keloGuo/magicKey63FW/image/PCB反面.jpg

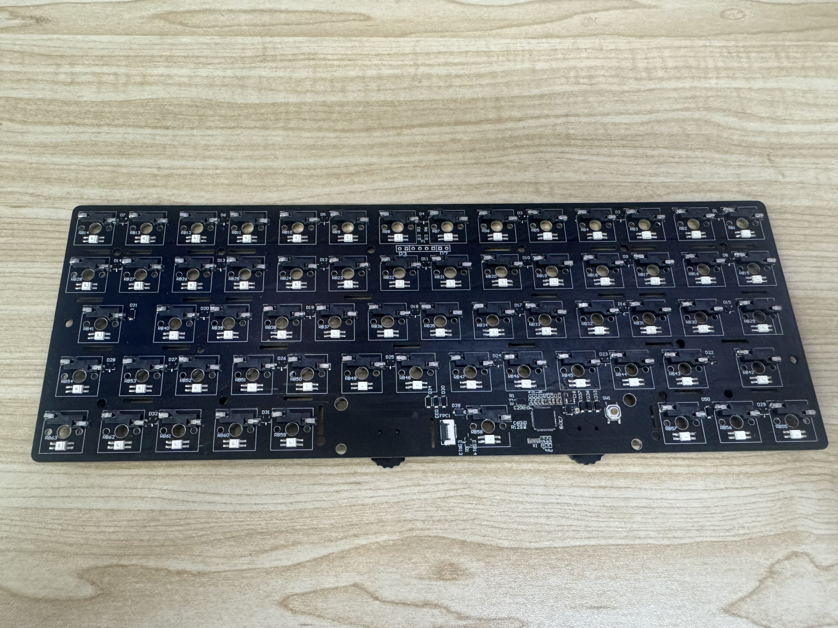
image/PCB反面.jpg
