keloGuo/magicKey63FW/image/web宏编辑页.png

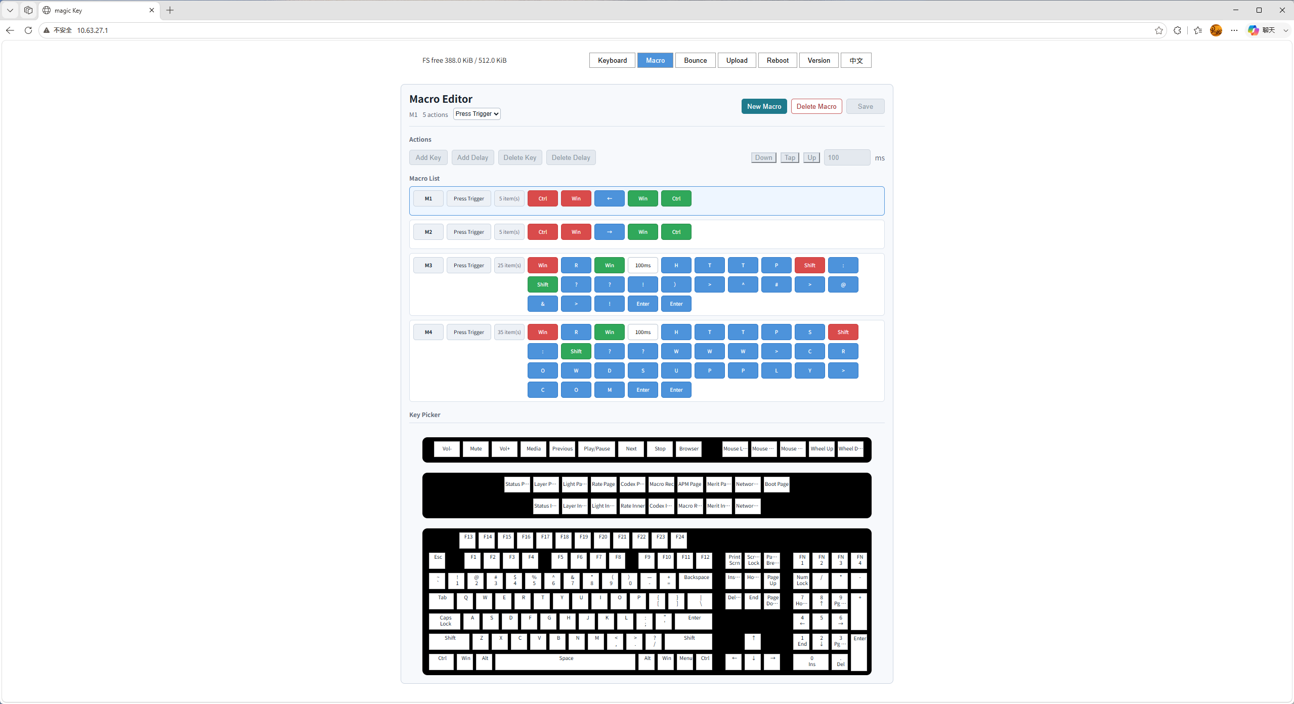
image/web宏编辑页.png
