keloGuo/magicKey63FW/image/定位板正面.jpg

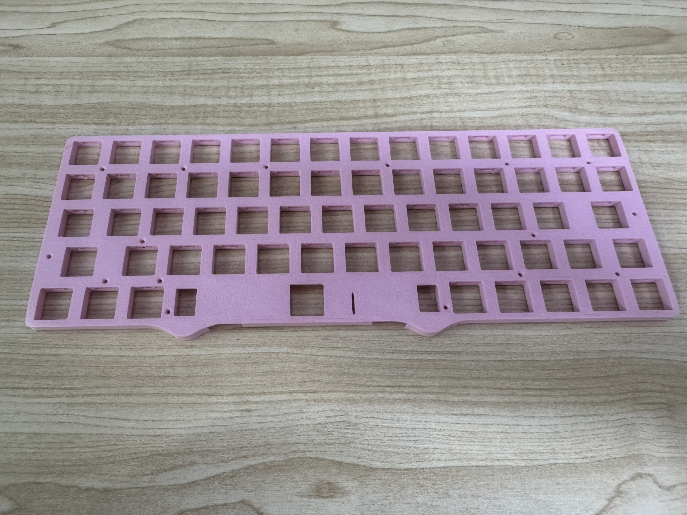
image/定位板正面.jpg
