keloGuo/magicKey63FW/image/定位板背面.jpg

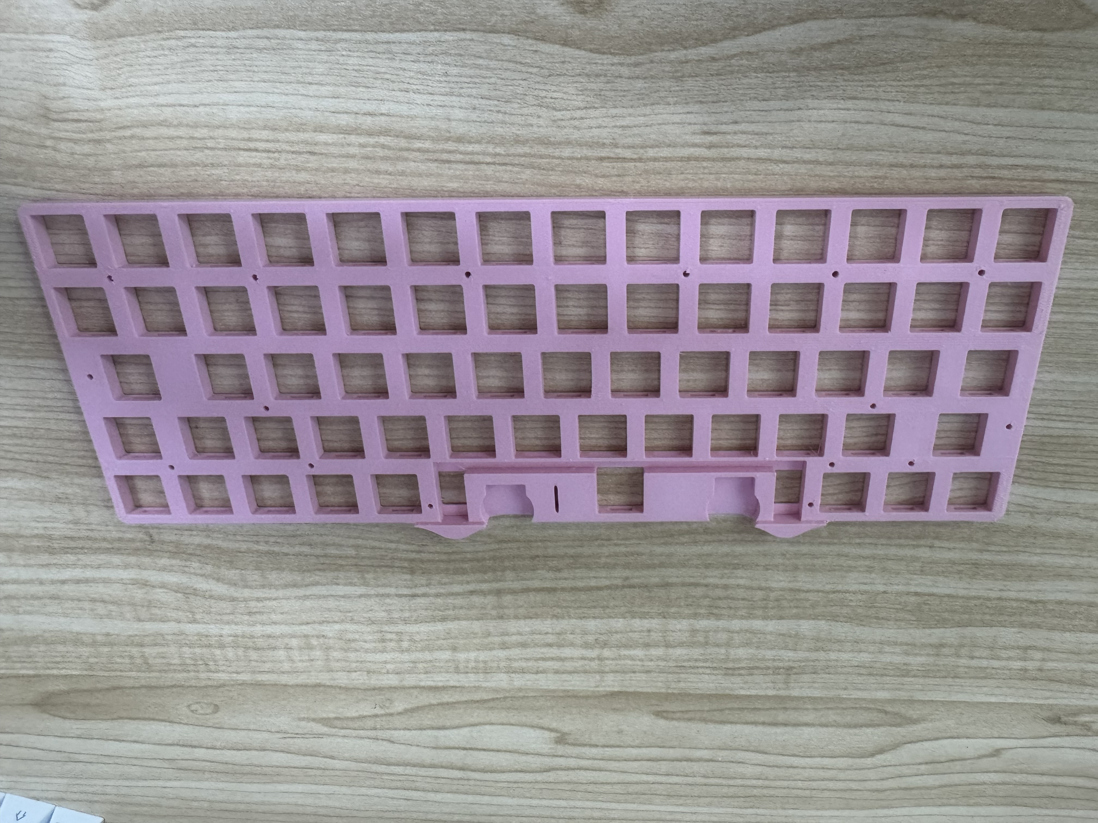
image/定位板背面.jpg
