keloGuo/magicKey63FW/image/底壳正面.jpg

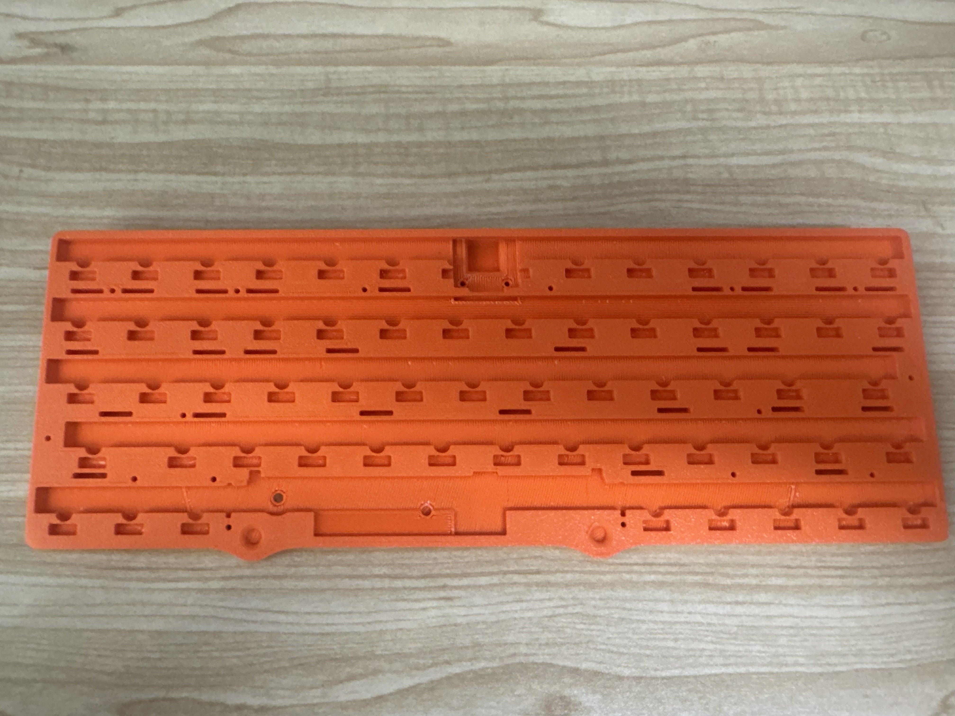
image/底壳正面.jpg
